GrayHatGuy/Xiao-esp32s3-lora-repeater/V8.2-SPEC.md

# V8.2-SPEC.md — RX-priority router backport + source-identity preservation

**Status:** ✅ BENCH-VERIFIED on branch `v8.2-router-backport` (off `main` @
`4b98a8d`), decisions locked §10. Pipeline backport + identity layer + §15.1
packet_id dedup all code-complete, build green (`pio run -e xiao_esp32s3`,
RadioLib 7.7.0, Flash ~24.5% / RAM ~18.6%), and **validated on hardware
2026-06-13**: §9 Phase A tests 1–9 passed on air (Test 10 jam-expiry accepted on
review), plus §15.1. A 5-dimension adversarial review ran over the diff (1
low-severity finding fixed, 6 refuted). **Remaining: merge → `main`, annotated
`v8.2` tag, push (owner-gated outbound).**
**Target:** `main` @ `4b98a8d` (v8.1 + docs) → release tag **v8.2** after bench verification.
**Author:** GrayHatGuy · designed 2026-06-12, implemented 2026-06-13
**References:**
- [`ROUTING-REDESIGN.md`](https://github.com/GrayHatGuy/Xiao-esp32s3-lora-repeater/blob/T_LORA_QUAD_ROUTE/ROUTING-REDESIGN.md) (branch `T_LORA_QUAD_ROUTE` @ `1de6a65`) — the design being backported
- `V8-SPEC.md` — the v8 portal/config architecture this builds on
- Bench precedent: the branch's **host SX1262 (R1/R2) side was validated end-to-end on hardware 2026-06-07** (MC↔MT both directions, text+telemetry, hash-dedup loop-drop, clean bodies, TX-done-timeout recovery). That validation is the backbone of this backport's risk argument.

---

## 1. Purpose & scope

Bring the RX-priority routing redesign (route queue + CAD listen-before-talk +
content-hash dedup + airtime throttle) from the unreleased 4-radio
`T_LORA_QUAD_ROUTE` branch onto the **shipping 2-radio dual-SX1262 design**
(`main`, v8.1), and add a **source-identity preservation layer** so a bridged
repeat carries (or reconstructs) the original sender's node ID and protocol
instead of appearing to come from the bridge.

**In scope:** everything host-side that touches the SX1262 path (R1/R2).
**Out of scope (explicitly):** all LR1121/co-processor material — `UartLink`,
`LinkProtocol`, `RemoteRadio`, `WioLR1121`, `RadioProfile`, the
`coproc-tlora-dual/` firmware, BridgeConfig schema v6, the 4-radio portal UI,
and the routing matrix. LR1121 functionality is unproven (RX deficit
investigation ongoing); none of it lands in v8.2. BridgeConfig stays at
**schema v4 — no NVS migration**, so an upgraded v8.1 device keeps its config.

**Versioning note:** a `v9.0` tag exists but lives on the `lr1121-phase1`
branch lineage (Phase-1 LR1121 bring-up), not on `main`. `main`'s latest
release tag is `v8.1`, so `v8.2` is the correct next tag for this line.

---

## 2. Audit — branch changes relevant to SX1262 NOT captured in ROUTING-REDESIGN.md

Audited: committed branch state `origin/T_LORA_QUAD_ROUTE` @ `1de6a65` diffed
against `main`. (The branch working tree also holds uncommitted changes — a
stray blank line in the root `platformio.ini` and LR1121 RX diagnostics + a
RadioLib 7.4.0 pin in `coproc-tlora-dual/` — reviewed and confirmed
out-of-scope: co-proc/LR1121 only.)

| # | Finding | In spec §3? | v8.2 action |
|---|---|---|---|
| A1 | **RadioLib version**: `main` pins `^6.6.0`; the branch host (where the new TX/CAD path was built AND bench-validated) pins **7.7.0**. The known 7.7.0 RX deficit is **LR11x0-specific**; the SX1262 path was proven good on 7.7.0 at the 2026-06-07 bench. | No | **Pin 7.7.0** (recommended — it is the bench-validated combination; staying on 6.6.0 would make v8.2 the untested combo). Owner decision §10-Q1. |
| A2 | **Chip-select park fix** (`db98740`): a disabled local SX1262 left its CS floating, corrupting the other radio's `begin()` (bench-observed CHIP_NOT_FOUND/FATAL). v8.1 happens to be safe today only because it constructs both wrapper objects unconditionally (ctor parks CS); the ported setup() constructs only enabled radios, so the explicit park is required. | Bench note only | Port: park both NSS pins HIGH at the top of setup() (`main.cpp` branch lines ~869-870). |
| A3 | **NodeDB thread-safety** (from Stage C `e361ae0`): internal mutex + copy-based `lookupShortName(nodeId, out, outCap)` (pointer-returning API removed). v8.1's "only radio1Task touches NodeDB" assumption breaks under the new pipeline and the identity layer (both tasks read it). | No | Port branch `NodeDB.{h,cpp}` verbatim. |
| A4 | **Freq-aware same-channel guard** (`be6329e`): portal guard relaxed to reject a same-protocol pair only when channel name+key **and frequency** all match. Needed to configure the same-protocol cross-frequency relay (the transparent-repeat use case, §5). | No | Port to the 2-radio guard in `CaptivePortal.cpp`. |
| A5 | **Review hardening inside the ported files**: `volatile _txInFlight`; `_rxFlag` cleared inside the SPI mutex in `scanChannel()`; TX-done **timeout recovery** (10 s) in the scheduler; DUTY=0 division guard; dedup table sized 512; `randomSeed(esp_random())` so co-located bridges don't CSMA-backoff in lock-step. | Partially (§8 as-built) | All arrive automatically with the verbatim ports. |
| A6 | **NodeInfo for both MT radios**: v8.1 only radio1Task advertises NodeInfo (R2=MT never does); the branch's generic task advertises on every MT radio. | No | Arrives with the generic radioTask. Small behavior change — flagged. |
| A7 | **RNS pacing knobs removed**: `BRIDGE_RNS_FRAG_DELAY_*` deleted; queued fragments are paced by the airtime throttle instead of inline `vTaskDelay`. | §8 (as-built map) | Arrives with the port; platformio.ini knob docs updated. |
| A8 | **Console log mutex** — identified at bench (cross-core `Serial.printf` interleave garbles the monitor; cosmetic, logging only). NOT implemented on the branch (no-code-changes directive). The 2-radio build has the same two-cores-two-tasks layout. | Bench close-out item | Proposed v8.2 addition (small): a `logf()` wrapper taking a mutex. Owner decision §10-Q4. |
| A9 | `MeshDecoderDebug.h` / `MeshEncoderDebug.h`: **identical** between main and branch — no decoder/encoder port needed. (The identity layer of §5 adds new encoder capability; that is new work, not a port.) | — | — |
| A10 | Radio task stack 8192: already on main (no change). | — | — |

---

## 3. Components ported from ROUTING-REDESIGN.md §3 (adaptation map)

The branch host implementation is taken **verbatim wherever possible** — that
code is exactly what passed the 2026-06-07 SX1262 bench. Adaptation is
confined to `main.cpp` (4 slots → 2, routing matrix → fixed crossover).

| Component | Source (branch) | v8.2 adaptation |
|---|---|---|
| **3.1 Hash dedup** (replaces the `[MT]/[MC]/[rns]` marker) | `src/DedupCache.{h,cpp}` | Verbatim. Plus one addition for §5: a raw-packet hash variant (see §6). |
| **3.2 Route queue** (per-destination, PSRAM-backed, age-bounded, drop-oldest) | `src/RouteQueue.{h,cpp}` | Verbatim. Its `#include "LoraRadio.h"` is satisfied because we adopt `LoraRadio.h` (below). 2 queues instead of 4. |
| **3.3 TX scheduler + CAD** (pop → CAD → non-blocking send, CSMA backoff, RX-strictly-first) | `src/main.cpp` `radioTask` (D-step) | Verbatim logic; `NR=2`; per-radio state arrays sized 2. The co-proc TX_DONE gate does not apply (no remote radios). |
| **§4 keystone — non-blocking TX** | `src/WioSX1262.{h,cpp}` (`scanChannel`/`startTransmit`/`txDone`/`finishTransmit`; SPI mutex released for the on-air time) | **Verbatim**, including adopting `LoraRadio.h` (abstract interface + shared `LoraConfig`/constants). Keeping the file byte-identical to the bench-validated version is deliberate — zero adaptation variables. (The co-proc keystone half is out of scope.) |
| **§6 airtime throttle** (task #2) | `estimateAirtimeMs` + duty-cap scheduling in `main.cpp` | Verbatim. |
| **Pipeline core** | `ingestAndFanout` / `enqueueTextForDest` / `enqueueReticulumForDest` | Ported with fan-out reduced to "the other radio" (no routeMask in schema v4). The §5 identity layer hooks in here. |

Notes:
- Adopting `LoraRadio.h` on a 2-radio build costs ~90 lines of interface and
  buys: byte-identical `WioSX1262`, a working `#include` for `RouteQueue`, and
  far less friction for any future merge with the quad line. It contains one
  LR1121 constant (`LR1121_TCXO_VOLTAGE`) — inert, kept for file identity.
- `NodeDB` is **no longer write-only** as on the branch: §5 re-purposes it as
  the MT identity source for cross-protocol attribution (the exact "future
  attribution feature" it was kept for).
- XIAO ESP32-S3 PSRAM: `RouteQueue` already falls back to internal RAM if
  `ps_malloc` fails; at depth 64 × ~262 B ≈ 17 KB per queue this is safe either
  way. The boot log prints which pool was used — recorded at bench.

---

## 4. Challenge analysis — why identity is lost, and what each protocol allows

The redesign strips the `[MT !id name]`/`[MC]` marker (clean far-side bodies),
so a bridged repeat is emitted under the **bridge's own identity** (MT) or
**no identity at all** (MC). What each side structurally offers:

- **Meshtastic** (decoder `MeshDecoderDebug.h:193-198`, encoder
  `MeshEncoderDebug.h:116-200`): the 16-byte cleartext header carries
  `src` (4 B) and `packet_id` (4 B). The encoder **already takes `srcNodeId`
  as a parameter**, and `encodeMeshtasticNodeInfo()` can mint a NodeInfo for
  **any** identity. The AES-CTR nonce is built from `packet_id`+`src` only, so
  preserving those two fields keeps ciphertext valid across header edits, and
  re-encrypting the same Data payload for a different channel key is possible
  without touching the protobuf. Native MT nodes dedup floods on (src,
  packet_id) and relayers decrement `hop_limit` (flags byte layout per the
  captured-packet analysis at `MeshEncoderDebug.h:167-171`; relay semantics to
  be **cited from Meshtastic firmware docs during implementation and proven at
  bench** — they were argued, not cited, in the branch review).
- **MeshCore GRP_TXT** (encoder `MeshEncoderDebug.h:44-108`): plaintext is
  `[ts:4][flags:1][body…\0]` — **no sender-identity field exists in the
  packet**. Identity rides *inside the body by convention*: real MeshCore
  clients send `"<name>: <text>"` (this is why v8.1's MC marker stayed bare —
  `main.cpp` comment "MC packets already carry the sender's name inline").
  So on the MC side, attribution can only ever be body-level text.

**Conclusion:** same-protocol identity preservation can be *exact* (carry the
original header). Cross-protocol preservation must be *reconstructed*: a
**deterministic virtual MT node** per MC sender (MC→MT), and a **name-prefix
body convention** (MT→MC). That is the design below.

---

## 5. Identity-preservation layer (the v8.2 feature)

Master switch `BRIDGE_IDENTITY_PRESERVE` (default **1**; `0` reproduces the
branch's clean-body/bridge-id behavior exactly).

### 5.1 Same protocol, same channel (name+key match, different frequency) — **transparent raw repeat**
The cross-frequency relay the freq-aware guard (A4) unlocks.

- **MT→MT:** re-transmit the **original bytes**, modifying only:
  `hop_limit` (flags[2:0]) decremented — packet with `hop_limit == 0` is
  **not** repeated; `relay_node` (byte 15) set to the bridge ID's low byte.
  `src`/`packet_id`/ciphertext untouched ⇒ far side sees the **original
  sender natively** — including **position, telemetry, and NodeInfo packets
  passed through in full fidelity** (no text-ification), and native (src,pid)
  dedup works. Packets with `src == bridge id` are skipped (self-echo).
  Only packets whose `channel_hash` matches the configured channel are
  repeated (conservative; "promiscuous repeat" noted as future option).
- **MC→MC:** re-transmit the original bytes **unchanged** (header, path, MAC,
  ciphertext). The body's native `"name: text"` arrives intact ⇒ identity
  preserved. *Open point:* a native MC repeater appends its hash to `path`;
  whether to mimic that needs a MeshCore-source citation — v8.2 ships
  unchanged-bytes repeat and records the question (§10-Q5).

### 5.2 Same protocol, different channels (different key) — **re-encrypt, preserve header**
- **MT→MT:** decrypt the Data payload with the source channel key (nonce =
  original pid+src), re-encrypt with the destination key, set the destination
  `channel_hash`, keep `src` and `packet_id`, decrement `hop_limit`.
  Identity exact; payload fidelity full (any portnum). New small helper in
  `MeshEncoderDebug.h` ("trans-crypt"); existing callers unchanged.
- **MC→MC:** decode (we already do), re-encode GRP_TXT with the destination
  key preserving `ts` and the body verbatim — `"name: text"` carries identity.

### 5.3 Cross-protocol MC→MT — **virtual node mapping**
- Parse the MC body's leading `"<name>: "` (1–40 printable chars, no ':').
- `virtualId = FNV-1a32("MC|" + name)`; re-hash on collision with reserved
  values (`0x00000000–0x000000FF`, `0xFFFFFFFF`) or the bridge's own ID.
  (Deterministic ⇒ the same MC sender maps to the same MT node across reboots
  and even across multiple bridges. 32-bit collision with a real node is
  possible but negligible at mesh scale — documented residual risk.)
- Emit the MT text with `src = virtualId` and the **name stripped from the
  body** (identity moved from text into the header where MT wants it).
- **`VirtualNodeMap`** (new, RAM-only, 32-entry LRU): name → virtualId +
  last-NodeInfo time. On first sighting and every
  `BRIDGE_VIRT_NODEINFO_PERIOD_MS` (default 15 min, only while active),
  enqueue a synthetic NodeInfo: `id="!<hex>"`,
  `long_name="<name> @MC"`, `short_name=` first 4 chars — so MT clients
  display the message from `Alice @MC`, not from the bridge.
- **No name parsed** ⇒ fall back to today's behavior (bridge identity, clean
  body). (§10-Q3 offers a per-channel catch-all virtual node instead.)
- Trust note: MC group identity is body text — anyone on the channel can claim
  any name. Virtual nodes are **display-level attribution at the same trust
  level as MC group chat itself**, stated plainly in README.

### 5.4 Cross-protocol MT→MC — **name-prefix convention**
- Resolve the MT `src` via NodeDB (short name; fallback `"!<8hex>"` — the
  32-bit origin ID stays recoverable in that form).
- Emit body `"<name>@MT: <text>"` (with `BRIDGE_TAG_ORIGIN_PROTO=0`:
  `"<name>: <text>"`, indistinguishable from a native MC sender).
- This is the only channel MC offers (no header identity field); it is
  attribution, not authentication.

### 5.5 Provenance summary ("nodeID/protocol known after repeat")
| Path | Node ID after repeat | Protocol provenance |
|---|---|---|
| MT→MT | exact (native header) | implicit (same protocol) |
| MC→MC | exact (native body/name + path) | implicit |
| MC→MT | deterministic virtual MT node per sender name | `@MC` suffix in NodeInfo long_name |
| MT→MC | name (+`!hexid` fallback) in body prefix | `@MT` suffix in body prefix |

---

## 6. Dedup / loop-safety interplay (analysis)

The DedupCache contract — record on RX *and* on every emission, drop on hash
match — is preserved under every §5 path:

| Path | Ingest records | Emission records | Echo of our TX hashes as | Result |
|---|---|---|---|---|
| Text re-encode (today) | h(body, srcId) | h(body, dstSrcId) | emission hash | drop ✓ |
| MT raw repeat | h_raw = FNV1a(src‖pid) | (same as ingest) | h_raw (src/pid unchanged; mutable bytes flags/next/relay excluded from hash) | drop ✓ |
| MC raw repeat | h_raw = FNV1a(mac[2]‖ciphertext) | (same) | invariant even if a native repeater extends `path` | drop ✓ |
| MT→MT trans-crypt | h_raw(src‖pid) | h_raw(src‖pid) (unchanged) | same | drop ✓ |
| MC→MT virtual | h(fullBody, 0) | h(strippedBody, virtualId) | emission hash | drop ✓ |
| MT→MC prefixed | h(body, mtSrc) | h(prefixedBody, 0) | emission hash | drop ✓ |

The accepted MeshCore limitation (content-only dedup: two different MC senders
sending identical text inside the TTL lose the second bridged copy) is
**improved** when a name is parsed — the name participates via the body — and
unchanged otherwise.

---

## 7. File-by-file change map

| File | Change | Provenance |
|---|---|---|
| `src/LoraRadio.h` | **new** | branch, verbatim |
| `src/WioSX1262.h` / `.cpp` | non-blocking TX + CAD; inherits `LoraRadio` | branch, **verbatim** |
| `src/DedupCache.h` / `.cpp` | **new**; + `hashRaw()` helper for §5.1 | branch verbatim + small addition |
| `src/RouteQueue.h` / `.cpp` | **new** | branch, verbatim |
| `src/NodeDB.h` / `.cpp` | mutex + copy-based lookup | branch, verbatim |
| `src/VirtualNodeMap.h` / `.cpp` | **new** — §5.3 map + synthetic-NodeInfo pacing | new code |
| `src/MeshEncoderDebug.h` | optional `pid` param on `encodeMeshtasticText`; MT trans-crypt helper; **existing call sites unchanged** | new code |
| `src/main.cpp` | rewrite to the branch pipeline at NR=2: generic `radioTask(i)`, `ingestAndFanout` + identity layer, TX scheduler, airtime throttle, CS-park, `randomSeed`; marker functions removed | branch structure + §5 |
| `src/CaptivePortal.cpp` | freq-aware same-channel guard (2-radio form of `be6329e`) — only portal change | branch, adapted |
| `src/BridgeConfig.*` | **unchanged** (schema v4) | — |
| `platformio.ini` | RadioLib pin → `7.7.0` (Q1); document `BRIDGE_*` knobs (below) | branch, adapted |
| `CHANGELOG.md`, `README.md` | v8.2 entry; identity-layer + clean-bodies documentation | at release |

**New/ported build knobs** (all `-D` overridable; defaults as on the branch):
`BRIDGE_DEDUP_TTL_MS=60000`, `BRIDGE_DEDUP_TABLE_SIZE=512`,
`BRIDGE_ROUTE_QUEUE_DEPTH=64`, `BRIDGE_ROUTE_MAX_AGE_MS=30000`,
`BRIDGE_CAD_BACKOFF_MIN/MAX_MS=20/120`, `BRIDGE_TX_INFLIGHT_TIMEOUT_MS=10000`,
`BRIDGE_TX_DUTY_PERCENT=50`, `BRIDGE_TX_MIN_GAP_MS=0`.
New for §5: `BRIDGE_IDENTITY_PRESERVE=1`, `BRIDGE_TAG_ORIGIN_PROTO=1`,
`BRIDGE_VIRT_NODES_MAX=32`, `BRIDGE_VIRT_NODEINFO_PERIOD_MS=900000`,
`BRIDGE_MC_NONAME_VIRTUAL=0` (Q3 — 0=bridge-id fallback, 1=per-channel catch-all).
Removed: `BRIDGE_RNS_FRAG_DELAY_MT/MC_MS` (A7). No portal/schema additions in
v8.2 — identity knobs are build-flags first; portal exposure is future work.

---

## 8. Implementation plan (commit sequence — each commit builds green)

1. `feat(radio):` `LoraRadio.h` + `WioSX1262` non-blocking TX/CAD + RadioLib pin (A1)
2. `feat(bridge):` `DedupCache` + `RouteQueue`
3. `fix(nodedb):` mutex + copy-based lookup (A3)
4. `feat(bridge):` `main.cpp` RX-priority pipeline + airtime throttle + CS-park (A2) + `randomSeed` — marker removed, clean bodies (functional parity with the branch, at 2 radios)
5. `feat(identity):` `VirtualNodeMap` + encoder pid/trans-crypt + raw-repeat paths + freq-aware guard (A4) — the §5 layer
6. `feat(log):` structured tagged logging schema (§13) **+ the log mutex (A8) — bundled** (the single-line key=val format is only trustworthy if a line is emitted atomically across the two cores)
7. `docs:` CHANGELOG v8.2, README, spec status flip

*(LoRaWAN seam — DROPPED from v8.2 per Q6; deferred wholesale to v8.3, §14.)*

Build verification per commit: `pio run -e xiao_esp32s3` (plus any other
`platformio.ini` envs present). Nothing is pushed during implementation.

## 9. Bench verification plan (gate before tag/push)

**Phase A — redesign regression** (config: R1=MC 910.525/BW62.5/SF7,
R2=MT 906.875/BW250/SF11 — the already-validated bench profile):
1. Boot: both radios init; RouteQueue alloc line (PSRAM vs internal) recorded.
2. CS-park regression: set R2=None in portal → R1 still inits (the `db98740` scenario).
3. MT→MC text: MC client shows `"<name>@MT: <text>"`.
4. MC→MT text: MT app shows the message from `Alice @MC` (virtual node + NodeInfo), body clean.
5. Loop suppression both directions (co-located echo → `loop-drop` log; no storm).
6. Position/telemetry → text lines still bridge; MT NodeInfo upsert + self-echo drop.
7. CAD defers TX while the channel is keyed; CSMA backoff observed in log.
8. **RX-priority headline:** long SF11 TX on R2 while R1 takes a burst — zero R1 RX loss.
9. Airtime throttle paces a message burst per duty setting.
10. Queue max-age expiry under a jammed channel (stale drop counted).

**Phase B — same-protocol identity** (reconfig: R1=MT LongFast 906.875,
R2=MT LongFast on a second slot — guard must now accept it (A4)):
11. Raw repeat: far-side MT app shows the **original sender** (not the bridge).
12. `hop_limit` decrement visible in the sniffer log; a `hop_limit=0` packet is NOT repeated.
13. Position/NodeInfo pass through natively (original sender's name appears on the far mesh without bridge synthesis).
14. No loop storm co-located (raw-hash dedup holds).

**Phase C (optional/stretch):** MT→MT cross-channel trans-crypt (different
PSKs); MC→MC raw repeat with a second MC channel pair.

**Acceptance:** Phase A all-pass mandatory. Phase B 11/12/14 mandatory for the
identity layer; if B fails and the fix isn't immediate, ship v8.2 with
`BRIDGE_IDENTITY_PRESERVE=0` default (redesign-only release) and re-bench the
layer for v8.3 — the architecture cleanly permits that fallback.

## 10. Decisions (LOCKED — owner, 2026-06-13)

- **Q1 — RadioLib → ✅ pin host to `7.7.0`** (the bench-validated combo; SX1262 unaffected by the LR11x0 deficit).
- **Q2 — provenance tags → ✅ ON by default** (`BRIDGE_TAG_ORIGIN_PROTO=1`): `"Alice@MT: text"` (MT→MC) and `"Alice @MC"` (MC→MT NodeInfo long_name) so the origin protocol is explicit.
- **Q3 — MC sender with no parseable name → ⚠️ NOT explicitly confirmed.** Owner did not tick the "fall back to bridge identity" default. Resolution: implement BOTH behind a build flag **`BRIDGE_MC_NONAME_VIRTUAL`** — **default `0` = fall back to bridge identity** (today's behavior, conservative, reversible); `1` = per-channel catch-all virtual node (`"MC-<chan>"`). Flagged for a one-word owner confirm; default ships if no change requested.
- **Q4 — logging rework + console log mutex → ✅ YES, bundled** (commit 6, §13). Structured tagged schema + dedicated log mutex ship together.
- **Q5 — MC raw-repeat path-append → ✅ ship unchanged-bytes repeat**; investigate MeshCore-native `path` semantics (needs a source citation) in a later version.
- **Q6 — LoRaWAN seam → ✅ DEFER FULLY to v8.3.** No LoRaWAN code in v8.2 (not even the enum/constant). Seam + capture-only design fully mapped in §14 so v8.3 is turnkey. **No LoRaWAN content bridging ever — see §14 (architecturally precluded, not merely deferred).**

## 11. Risks

| Risk | Mitigation |
|---|---|
| RadioLib 6.6→7.7 host regression | The branch built+bench-passed the identical `WioSX1262` code on 7.7.0; full bench gate before release. |
| MT hop/relay/dedup semantics asserted, not yet cited | Cite Meshtastic firmware source during implementation; bench tests 11/12/14 prove behavior on air. |
| MC client rendering of `"name@MT: text"` | Verified on a real MC client at bench test 3. |
| Virtual-ID collision with a real MT node | ~1/2³² per (sender, node) pair; deterministic and documented; reserved ranges avoided. |
| False name-parse on MC bodies containing `": "` | Parse bounds (≤40 printable chars); worst case = cosmetic mis-attribution of that one message; master switch available. |
| Dedup TTL false-drop (identical text, two senders, no id) | Inherited accepted limitation (MC only); improved when names parse. |
| No PSRAM on a given board | RouteQueue falls back to internal RAM (~17 KB/queue at depth 64). |

## 12. Release process (after bench approval)

1. Owner approves bench results.
2. `CHANGELOG.md` v8.2 entry + README finalized; this spec's status flipped to AS-BUILT.
3. Commit, **annotated tag `v8.2`** on `main`, push `main` + tag (normal push — never force-push `main`).
4. GitHub release notes drafted from the CHANGELOG — **owner reviews before publishing** (outbound gate).

---

## 13. Serial debug logging schema (v8.2) — owner Q1

**Decision:** adopt the owner's field set and extend it; replace the ad-hoc
`[%8lu ms][%s ...]` prose lines with a **single greppable, tagged `key=val`
line per event**, and ship a **dedicated log mutex** (separate from `spiMutex`)
so a line emits atomically across both cores. The heavy hex/protobuf decoder
dump (`MeshDecoderDebug::print`) stays its own multi-line block, preceded by an
`evt=RX` header so a parser can still anchor it.

**Why split the owner's one line into a few events:** the pipeline decodes +
dedups ONCE (`ingestAndFanout`, one `DedupCache::seenAndRecord`), then fans out
to up to N−1 destinations, each of which encodes → records-emit-hash → pushes,
after which a *separate* radio task (possibly on the other core) pops → CADs →
transmits → throttles. One line can't honestly carry all of that, so a small
enumerated `evt` tag set is used. It is a strict **superset** of the owner's
intent: "radio-emitted-or-drop" = `evt` + a `drop=` token; "hash ingested" /
"hash emitted" = `hin=` / `hout=` on the right events.

**Format:** every line starts `ts=<ms> evt=<TAG> radio=<R1|R2>` then only the
keys valid at that stage. `evt` ∈ {`RX`, `DEDUP_PASS`, `DROP`, `QUEUE`, `CAD`,
`TX_START`, `TX_DONE`, `THROTTLE`, `NODEDB`, `NODEINFO`}.

| Key | Stage | Source (ported `main.cpp`) | Notes |
|-----|---|---|---|
| `ts` | all | `millis()` | leading key, always first |
| `evt` | all | synthesized | the parseable event tag |
| `radio` | all | `kTag[i]` | RX radio for ingest; owning radio for TX-side |
| `proto` | RX | `g_chan[i].protocol` | `MC`/`MT`/`RNS` — disambiguates the id fields |
| `rssi`,`snr` | RX | `read(buf,len,&rssi,&snr)` | **added** — the key weak-RX bench fields the owner's list omitted |
| `len` | RX/TX | RX `len`; emitted `outLen` | RX truncation / airtime input |
| `nodeid` | RX | `buf[4..7]` (MT, `len≥8`) | owner's "nodeid"; **MT-only**, else `-` |
| `hin` | DEDUP | `DedupCache::hash(body,len,srcId)` | owner's "hash ingested"; logged on PASS and on `drop=loop-dup` |
| `drop` | DROP | enumerated branch | `loop-dup`/`rns-dup`/`self-echo`/`encode-fail`/`queue-full`/`frag-overflow`/`cad-busy`/`tx-startfail`/`tx-timeout` — a **token**, not prose, so loss is grep/awk-histogrammable |
| `dst` | QUEUE/TX | dest index `j`/`destIdx` | owner's "radio emitted"; without it a fan-out leg is unattributable |
| `virtualid` | IDENTITY | `dstSrcId` stamped on the re-encode | owner's "virtualid"; **MT-only** (0/`-` for MC by design) |
| `hout` | QUEUE | `DedupCache::hash(body,len,dstSrcId)` recorded pre-push | owner's "hash emitted"; lets a `loop-dup` be matched offline to our prior emit |
| `qdepth`,`qdropped` | QUEUE | `RouteQueue::count()`/`dropped()` | **added** — surfaces stale-age/overflow loss that is otherwise silent (one-line getters if not yet public) |
| `cad`,`backoff` | CAD | `scanChannel()`, `g_txBackoffUntil[i]` | **added** — channel-contention vs TX failure |
| `air`,`gap`,`nexttx` | THROTTLE | `estimateAirtimeMs()`, `g_nextTxAllowedMs[i]` | **added** — a duty-cycle hold otherwise looks like a hang |
| `frag`,`seq` | QUEUE | RNS `idx/total`, `crc16` low byte | **added** (RNS only) — ties fragments together |
| `ni_id`/`ni_short`/`ni_long`, `selfid`/`selfname` | NODEDB/NODEINFO | `extractMeshtasticNodeInfo`→`NodeDB::upsert`; `BridgeConfig::mt*` | the MC→MT virtual-node + synthetic-NodeInfo trail (§5.3) |

Re-scope note: `nodeid` and `virtualid` are populated only for Meshtastic
(`srcId` parsed only when MT & `len≥8`; `dstSrcId` is deliberately 0 for
MeshCore). They are emitted as `-` otherwise so a logged `0` is never mistaken
for "sender id zero."

**Example lines:**
```
ts=120345 evt=RX radio=R1 proto=MC len=41 rssi=-92.5 snr=7.2 nodeid=-        # decoder dump follows
ts=120347 evt=DEDUP_PASS radio=R1 proto=MC hin=0x8f3a21c4 msg="hello mesh"
ts=120902 evt=DROP radio=R2 proto=MT drop=loop-dup nodeid=!a1b2c3d4 hin=0x5512ee07 msg="hello mesh"
ts=121050 evt=QUEUE radio=R2 dst=R2 virtualid=!7e10ff20 hout=0x44ab1290 len=58 qdepth=3 qdropped=0 msg="hello mesh"
ts=121051 evt=CAD radio=R2 cad=busy backoff=74
ts=121180 evt=TX_START radio=R2 cad=clear len=58 rc=0
ts=121180 evt=THROTTLE radio=R2 air=129 gap=258 nexttx=121438
ts=121309 evt=TX_DONE radio=R2 result=done air=129
ts=140502 evt=DROP radio=R1 proto=MT drop=self-echo ni_id=!7e10ff20
ts=300100 evt=NODEINFO radio=R2 op=mint selfid=!7e10ff20 selfname="XIAO-Bridge" len=72
```
A `loraview`/`awk` one-liner over `evt=DROP` then yields a per-cause loss
histogram — impossible with today's free-text lines. This logging is part of
the §9 bench gate, so it lands *before* bench (commit 6 in §8).

---

## 14. LoRaWAN (LoRa sync 0x34) — staging decision + design — owner Q2

**DECISION (locked 2026-06-13): deferred wholesale to v8.3 — no LoRaWAN code in
v8.2, not even the enum/constant seam.** This section is the v8.3 design of
record. The research below shows LoRaWAN is **not a smaller version of the
existing bridge** — bidirectional *content* bridging is architecturally
precluded, not merely deferred. So the future feature is a **capture-only RX
metadata tap**, not an MC/MT-style content bridge.

### 14.1 Why LoRaWAN content bridging is precluded (verified against LoRaWAN L2 1.0.x/1.1 + Semtech)
The existing bridge works because MeshCore (public channel) and Meshtastic
(default-key channel) both expose **group/broadcast text under a shared or
well-known key** — so the bridge can decrypt one side and re-encrypt for the
other. LoRaWAN breaks every premise of that model:
- **No group/broadcast/well-known key.** `FRMPayload` is AES-CTR encrypted
  under a **per-device `AppSKey`**; the 4-byte MIC is AES-CMAC under a per-device
  network key. A bridge without each device's provisioned session keys reads
  **zero** payload bytes. (Confirmed: even a real LoRaWAN *gateway* — the
  privileged node — forwards the raw PHYPayload and never decrypts; decryption
  happens only at the Network/Application server.)
- **Star topology, not a peer text mesh.** Frames are addressed to a network
  server via `DevAddr`, not to a human-readable channel. There is no "post to a
  public channel" primitive to map an inbound MC/MT message onto.
- **TX is undefined for the general case.** Emitting a frame any device accepts
  needs that device's `DevAddr` + `AppSKey` + network key + the correct next
  monotonic `FCnt` + correct uplink/downlink `Dir` + (for a Class A device) a
  real-time RX1/RX2 downlink window right after *it* transmits — i.e. you must
  *be* its network server. An inbound group-text string has no valid target.
- **What a keyless sniffer on 0x34 *can* read (cleartext):** `MType`, `DevAddr`
  (locally-assigned, not a stable hardware id, changes on re-join), `FCtrl`,
  `FCnt`, `FPort`, length, plus PHY metadata (RSSI/SNR/SF/freq). On **LoRaWAN
  1.0.x specifically, piggybacked `FOpts` MAC commands are also cleartext**
  (encrypted only in 1.1) — but those are network housekeeping, **not**
  application text. `DevEUI`/`JoinEUI` appear in clear only during the OTAA
  Join-Request.

(Sync-word confirmation: **0x34 is the LoRaWAN public sync word** on SX127x;
the SX126x programmed equivalent is `0x3444`. It is mutually distinct from
MeshCore 0x12 and Meshtastic 0x2B, so PHY-layer separation is clean — adding
0x34 RX is trivial at the radio-config layer; the difficulty is entirely above
the PHY.)

### 14.2 The honest future scope (v8.3+, NOT v8.2)
A **one-way capture/summarize tap**, analogous to the partial Reticulum capture
path: on a radio configured to LoRaWAN, decode the cleartext header and either
log it (§13 `evt=RX proto=LW devaddr=… fcnt=… fport=… rssi=…`) and/or emit a
**metadata** MC/MT text line (`"LoRaWAN: DevAddr 0x26011F8A FCnt 4213 FPort 2
SF7 -91dBm"`). This is situational awareness, explicitly **not** message
content. True content decode is possible *only* for the operator's own
provisioned devices (ABP / imported `AppSKey`) — that is "decrypt my own fleet,"
a separate optional feature, not "bridge LoRaWAN." **TX stays a permanent
log-and-drop** (`"No TX 2 LoRaWAN"`, mirroring the RNS-dest stub) — that is the
correct end state, not a placeholder.

### 14.3 The seam (Q6) — exact, fully mapped, so v8.3 is turnkey
The dispatch surface is sync-word-driven and clean. A future LoRaWAN protocol
touches (verified against this baseline):

| File | Change | Stub cost |
|---|---|---|
| `BridgeConfig.h` | `PROTO_LORAWAN` enum value | 1 line |
| `BridgeConfig.cpp` | sync→proto map: `0x34 → PROTO_LORAWAN` | 1 line |
| `MeshDecoderDebug.h` | `SYNC_WORD_LORAWAN = 0x34` constant (0x34 absent elsewhere) | 1 line |
| `MeshDecoderDebug.h` | capture decoder `printLoRaWAN()` (header-only) | v8.3 |
| `MeshEncoderDebug.h` | `encodeLoRaWAN()` stub → `return false` (permanent: no content TX) | 3 lines |
| `main.cpp` `ingestAndFanout` | RX case: capture/summarize (not text-extract) | v8.3 |
| `main.cpp` `enqueueTextForDest` switch | dest case → log-and-drop (like RNS dest) | 2 lines |
| `CaptivePortal.cpp` | protocol picker entry + sync lookup + RF defaults | ~5 lines, v8.3 |
| `LoraConfigCheck.h` | no change (sync is range-checked, accepts 0x34) | 0 |

**Two-tier seam:**
- **v8.2 (zero-risk, optional — Q6):** the enum value + the `0x34` constant
  *only*. No portal entry, no dispatch case. Reserves the address space, changes
  no behavior, touches only isolated declaration files — **zero conflict** with
  the pipeline rewrite.
- **v8.3 (the real feature):** portal entry + `printLoRaWAN` capture decode +
  the summarize-to-MC/MT path + permanent TX-drop.

**Conflict note:** the QUAD-branch audit suggested "add the stub to `main`
first, then cherry-pick." That assumed the *old* `bridgePacket()` dispatch. v8.2
**rewrites** that into `ingestAndFanout`/`enqueueTextForDest`, so the few
`main.cpp` seam lines must target the **new** pipeline — which is exactly why
the seam's `main.cpp` parts are deferred to v8.3 and only the isolated
declarations are eligible for v8.2. This avoids the merge conflict entirely.

---

## 15. Post-bench follow-ups (DEFERRED — implement after the bench gate)

### 15.1 Fold the Meshtastic packet_id into the MT dedup key — **✅ IMPLEMENTED + BENCH-VERIFIED 2026-06-13 (commit `cdd9803`)**
**Bench result (2026-06-13):** three identical `"ping"`s from one MT node (ids
3BD0/3BD1/3BD2) produced three *distinct* ingest hashes (0xd86b6427 / 0x4e7d113e
/ 0xe74827e0) → all three `DEDUP_PASS` and bridged (was 1 pass + 2 loop-dup
pre-fix). In the same capture, ping #2 (id 3BD1) **relayed back** matched its
ingest hash (0x4e7d113e) → `drop=loop-dup` — loop-safety intact. Design below.

**Observed at bench (2026-06-13):** a node sending the *same text twice* within
the 60 s dedup TTL has the second copy dropped as `loop-dup`. Live evidence: an
MT node (`!3d3a87a3`) sent `"l"` three times (distinct packet_ids
`0x3BB6/3BB7/3BB9`); the bridge **received all three** (`evt=RX` each) but
bridged only the first — the 2nd/3rd hit `drop=loop-dup` on the identical hash
`0x3d5964d8`. Same effect would hit a **stationary node's repeated identical
position/telemetry** if it broadcasts more often than the TTL. (This is a narrow
v8.2 behaviour change vs v8.1's marker scheme, which bridged each repeat. RX is
unaffected — the packets are received then intentionally deduped.)

**Root cause:** `DedupCache::hash` keys on `(decoded body + srcId)`, not the
Meshtastic `packet_id`, so two genuinely-distinct messages with identical
body+sender collide.

**Fix:** fold the MT `packet_id` into the dedup key for the Meshtastic path
only: key on `(body, src, packet_id)`.

**Why it stays loop-safe** (the load-bearing claim — cite Meshtastic firmware
when implementing): Meshtastic relays and flood-replays **preserve `(src,
packet_id)`** (that is how Meshtastic's own dedup works), so an echo/replay of a
foreign packet OR of our own emission still carries the same pid → the dedup
still matches and drops it. Only *genuinely new* user messages carry a *new*
pid → distinct hash → bridged. The on-air loop-drop already proven at bench
(`hin==hout`) keeps working because the relayed echo preserves the pid we
stamped.

**Scope / touch-points:**
- `DedupCache::hash` — add a folded 32-bit `pid` argument (or an overload);
  callers pass `pid=0` where there is none.
- **Ingest** (`main.cpp ingestAndFanout`, MT branch): parse `packet_id` from
  `buf[8..11]` (already parsed nearby for `srcId`) and fold it in.
- **Emission** (`enqueueTextForDest` MT path, `enqueueReticulumForDest` MT
  fragments): record `hash(outBody, dstSrcId, emittedPid)`. This requires
  `MeshEncoderDebug::encodeMeshtasticText` to **return the random pid it
  generates** (currently internal via `esp_random()` and not exposed) — add an
  out-param. The synthetic NodeInfo path is unaffected (not dedup-recorded).
- **MeshCore / RNS:** unchanged — GRP_TXT has no per-message id on the wire, so
  `pid=0` and MC-source identical-text repeats **remain** deduped (inherent
  accepted limitation; document it as such).

**Re-verify after implementing:** (1) send identical MT text 3× from one node →
all 3 bridge (no `loop-dup`); (2) a relayed echo of a bridged packet STILL
`drop=loop-dup` (loop-safety intact); (3) a stationary node's repeated identical
position within the TTL bridges each time; (4) two different MC senders, same
text, within TTL → 2nd still deduped (unchanged MC limitation).

### 15.2 (Cosmetic, optional) decoder-dump under the log mutex
`MeshDecoderDebug::print` still uses raw `Serial.printf`, so its multi-line
hex/protobuf dump can interleave with `blogf` lines across cores (observed at
bench as occasional garble like `[_APP) payld …`). The structured `evt=` lines
are atomic and unaffected. Wrapping the decoder dump would require threading the
log mutex into the decoder header (many printfs) — low value, deferred.
