GrayHatGuy/Xiao-esp32s3-lora-repeater/src/WioSX1262.h

#pragma once

#include <Arduino.h>
#include <SPI.h>
#include <RadioLib.h>
#include "LoraRadio.h"

// LoraConfig + the compile-time board constants now live in LoraRadio.h,
// shared by every radio wrapper.

class WioSX1262 : public LoraRadio {
public:
    WioSX1262(int nss, int dio1, int reset, int busy,
              int antSw, SPIClass &spi, SemaphoreHandle_t mutex,
              const char *name, const LoraConfig &config);
    ~WioSX1262() override;

    bool    begin() override;
    bool    available() override;
    int16_t read(uint8_t *buf, size_t &len, float *rssi, float *snr) override;
    int16_t transmit(const uint8_t *buf, size_t len) override;
    void    startReceive() override;

    // RX-priority CSMA extensions — see LoraRadio.h.
    int16_t scanChannel() override;
    int16_t startTransmit(const uint8_t *buf, size_t len) override;
    bool    txDone() override;
    void    finishTransmit() override;

    // Replace the RF plan for a runtime re-tune, then call begin() to apply it.
    // Used by the SX1262 co-processor (v8.5) when a CFG_RADIO frame arrives: the
    // static ISR registration done in the ctor is preserved (no reconstruction).
    void    setConfig(const LoraConfig &config) { _config = config; }

    // Written by the IRAM ISR trampoline; read by the polling task. The same
    // DIO1 line signals both RxDone and TxDone; _txInFlight tells them apart.
    volatile bool _rxFlag = false;

private:
    Module           *_mod;
    SX1262           *_radio;
    SemaphoreHandle_t _mutex;
    int               _antSw;
    const char       *_name;
    LoraConfig        _config;
    volatile bool     _txInFlight = false;   // non-blocking TX outstanding

    void _setAnt(bool tx);
};
